vipingupta642/ChargeControllerWithMPPT/Firmware/ChargerMPPT/app/inc/BasicInit.h

/********************************************************************************
 * project     Charge controller for solar panel with MPPT algorithm            *
 *                                                                              *
 * file        BasicInit.h                                                      *
 * author      Ila Galkin (aka Nordic Energy)                                   *
 * date        14.08.2019                                                       *
 * copyright   The MIT License (MIT). Copyright (c) 2019 Ilya Galkin            *
 * brief       Basic initialization for peripheral                              *
 *                                                                              *
 ********************************************************************************/

/********************************************************************************
 * Include 
 ********************************************************************************/

#pragma once 

#include "stm32f3xx.h"

#include "LedAndButton.h"
#include "SystemAndClock.h"

/********************************************************************************
 * Local function declaration
 ********************************************************************************/

void BasicInitPeripheral (void);

/********************************* END OF FILE **********************************/
